impatrq/Soleac/Carpeta de campo/Medidas_Antena/140426(1).jpeg

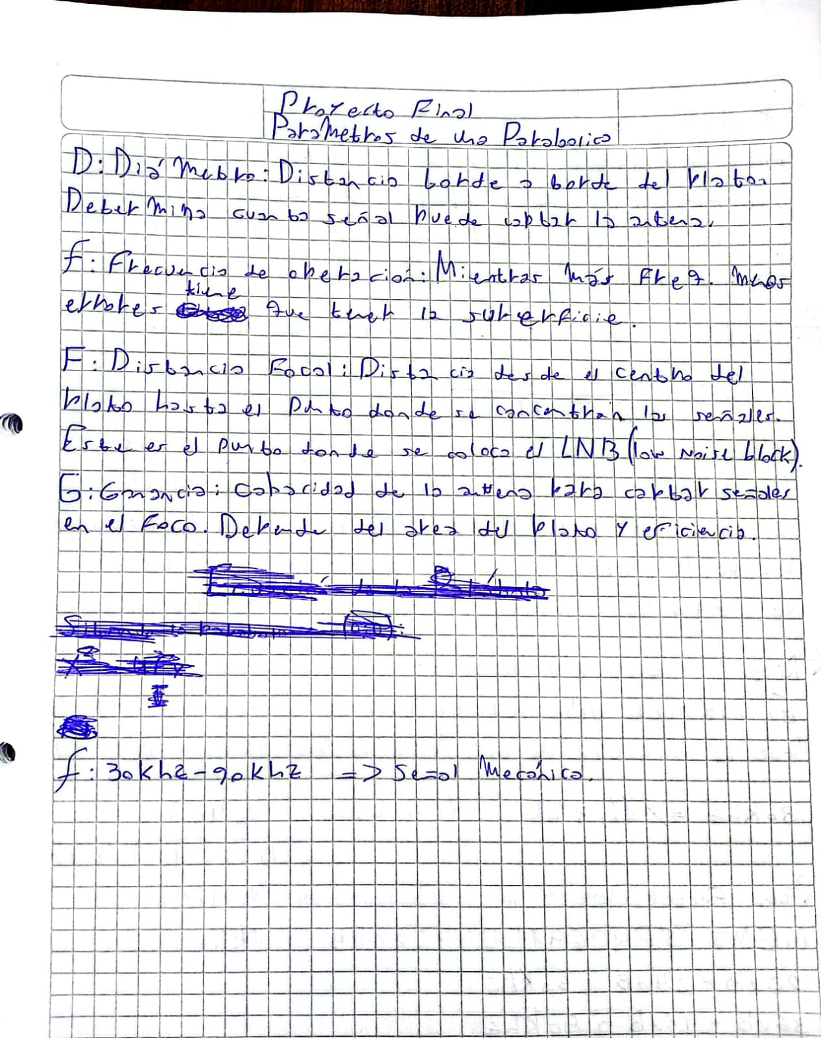
Carpeta de campo/Medidas_Antena/140426(1).jpeg
