impatrq/Soleac/Carpeta de campo/Medidas_Antena/140426(2).jpeg

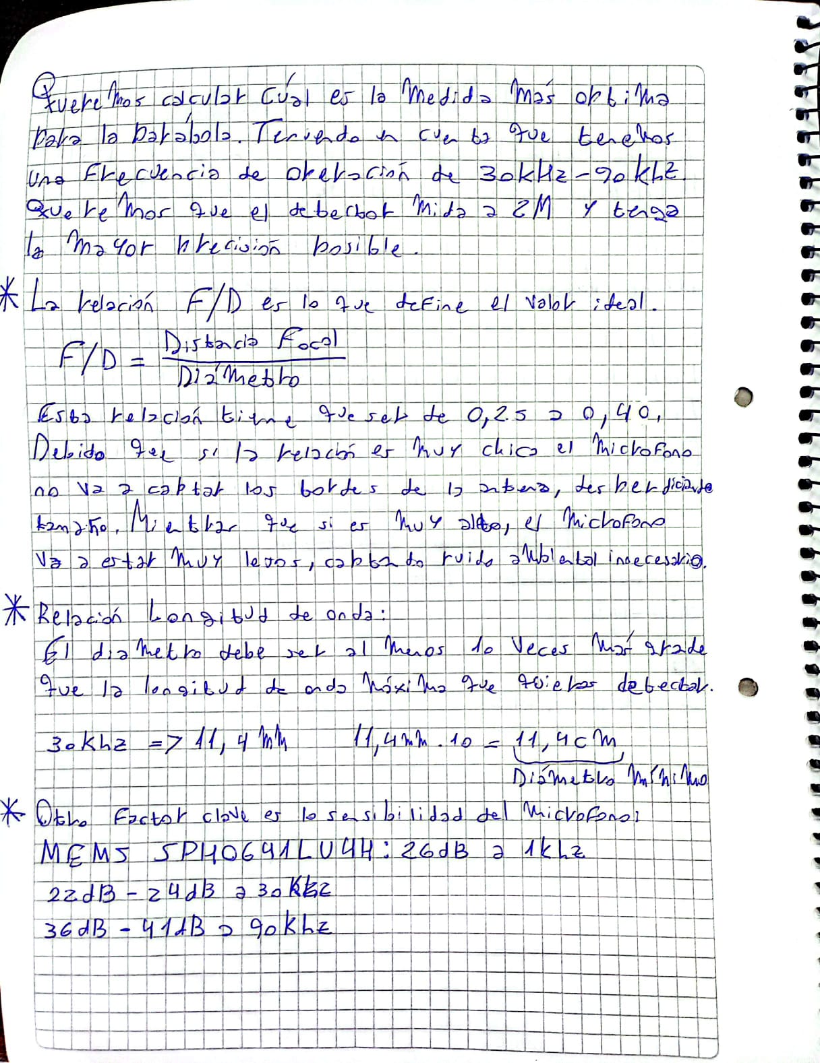
Carpeta de campo/Medidas_Antena/140426(2).jpeg
