impatrq/Soleac/Carpeta de campo/Medidas_Antena/140426(3).jpeg

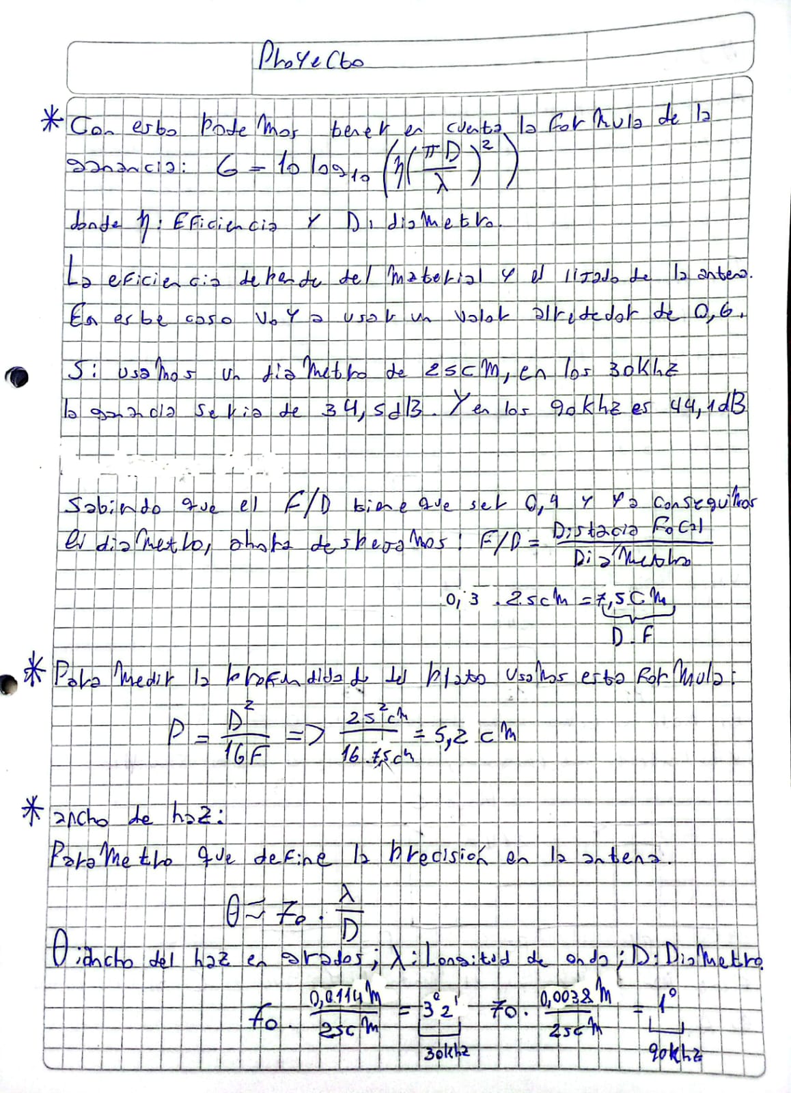
Carpeta de campo/Medidas_Antena/140426(3).jpeg
